fabiobaltieri/sensor-breakout/firmware/adc.c

/*
 * Copyright 2011 Fabio Baltieri (fabio.baltieri@gmail.com)
 *
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
 */

#include "board.h"

#include <avr/io.h>
#include <avr/interrupt.h>
#include <avr/sleep.h>
#include <util/delay.h>

#include "adc.h"

void adc_init(void)
{
	ADCSRA = ( (1 << ADEN)  | /* enable           */
		   (0 << ADSC)  | /* start conversion */
		   (0 << ADATE) | /* free running     */
		   (1 << ADIF)  | /* clear interrupts */
		   (0 << ADIE)  | /* interrupt enable */
		   (1 << ADPS2) | (1 << ADPS1) | (1 << ADPS0) );

	/* 12Mhz / 64 = 187.5kHz */
}

void adc_stop(void)
{
	ADCSRA = 0x00; /* ADC disable */
}

uint16_t adc_get(uint8_t cfg, uint8_t intref)
{
	if (intref)
		ADMUX = (1 << REFS1) | (1 << REFS0) | (cfg & 0x0f);
	else
		ADMUX = (0 << REFS1) | (1 << REFS0) | (cfg & 0x0f);

	/* wait signals to stabilize */
	_delay_ms(5);

	ADCSRA |= _BV(ADSC);

	loop_until_bit_is_clear(ADCSRA, ADSC);

	return ADCW;
}
